BjarniHeselmans/Bat-Detectie/Docs/Attachments/esp32-s2-mini2.jpg

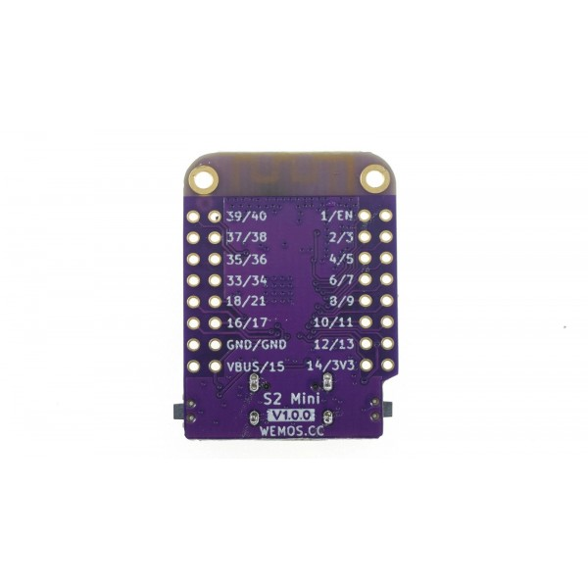
Docs/Attachments/esp32-s2-mini2.jpg
