BjarniHeselmans/Bat-Detectie/Docs/Attachments/esp32-s2-mini3.jpg

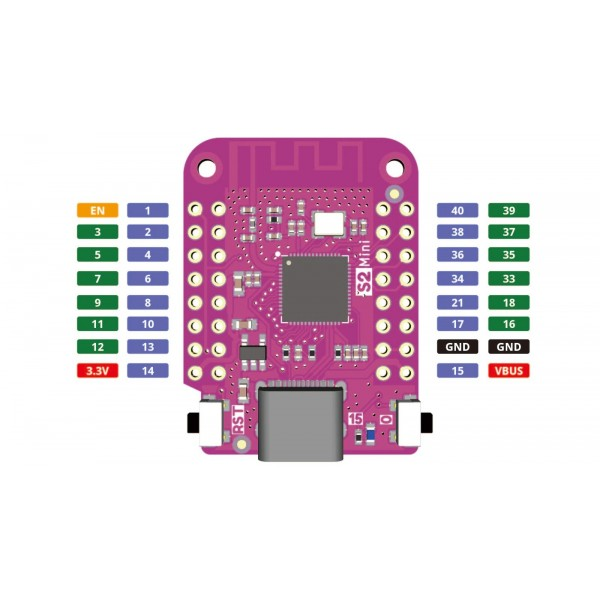
Docs/Attachments/esp32-s2-mini3.jpg
