BjarniHeselmans/Bat-Detectie/Docs/Attachments/esp32-s2-mini.jpg

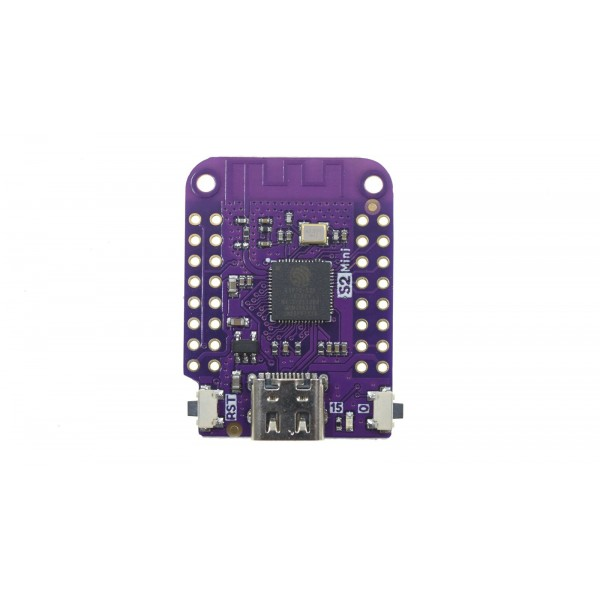
Docs/Attachments/esp32-s2-mini.jpg
