BjarniHeselmans/Bat-Detectie/Docs/Attachments/opstelling_Mini_v2.png

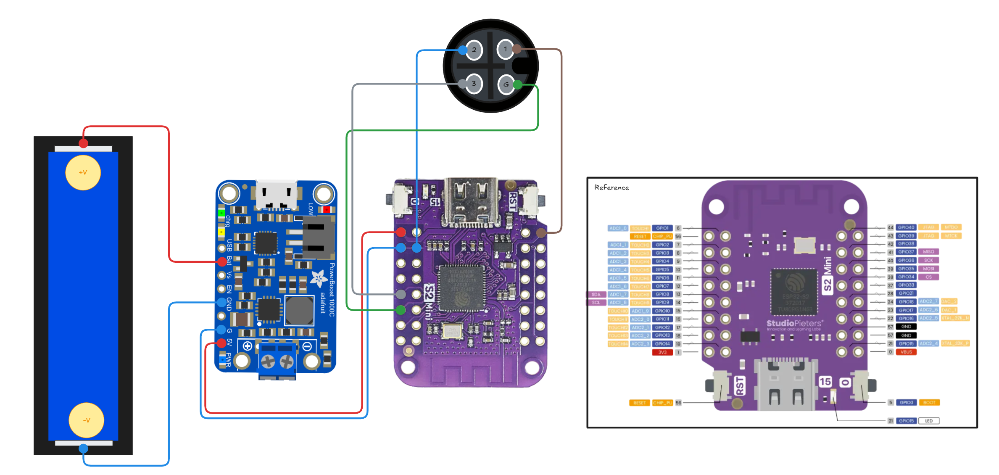
Docs/Attachments/opstelling_Mini_v2.png
