BjarniHeselmans/Bat-Detectie/Docs/Attachments/Opstelling_SHT3X.png

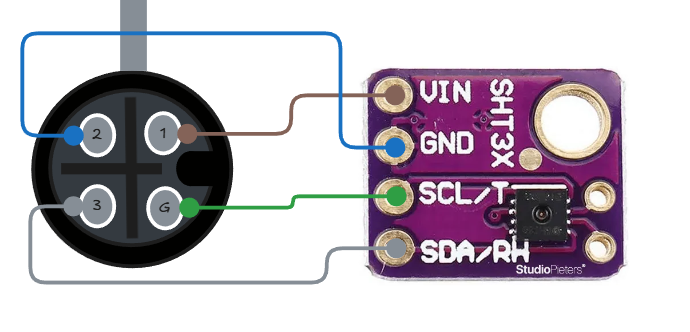
Docs/Attachments/Opstelling_SHT3X.png
