BjarniHeselmans/Bat-Detectie/Docs/Attachments/Overview.jpg

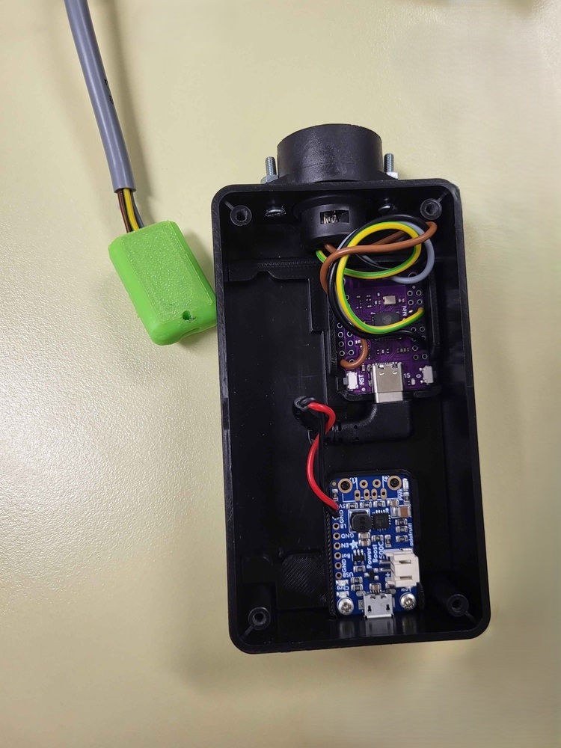
Docs/Attachments/Overview.jpg
