BjarniHeselmans/Bat-Detectie/Docs/Attachments/Power-Boost-5000.jpg

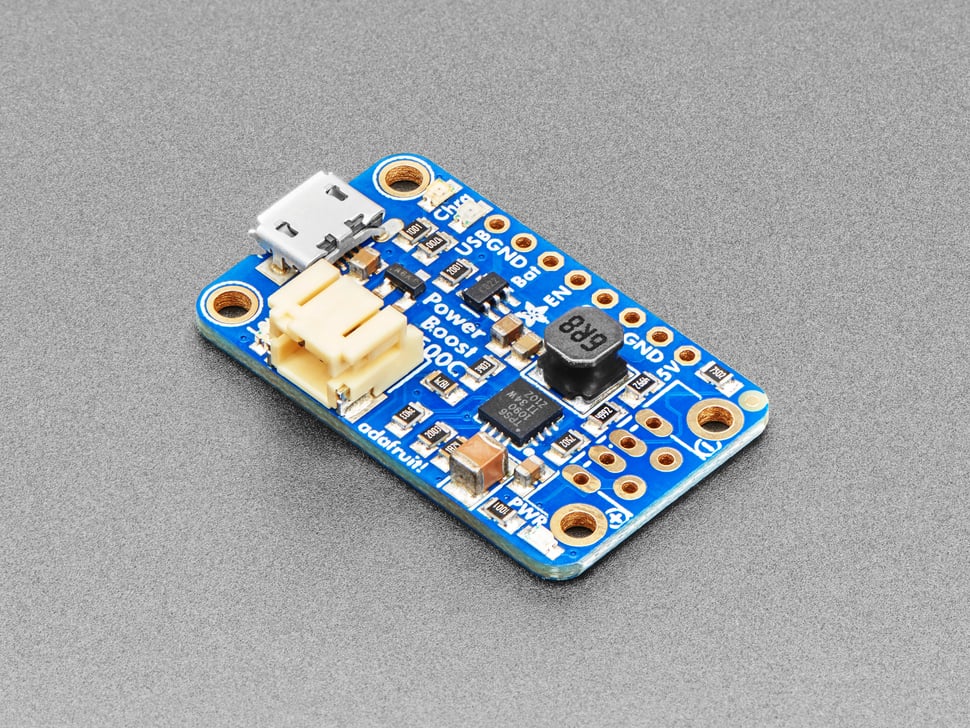
Docs/Attachments/Power-Boost-5000.jpg
