BjarniHeselmans/Bat-Detectie/Docs/Attachments/Power-Boost-50002.jpg

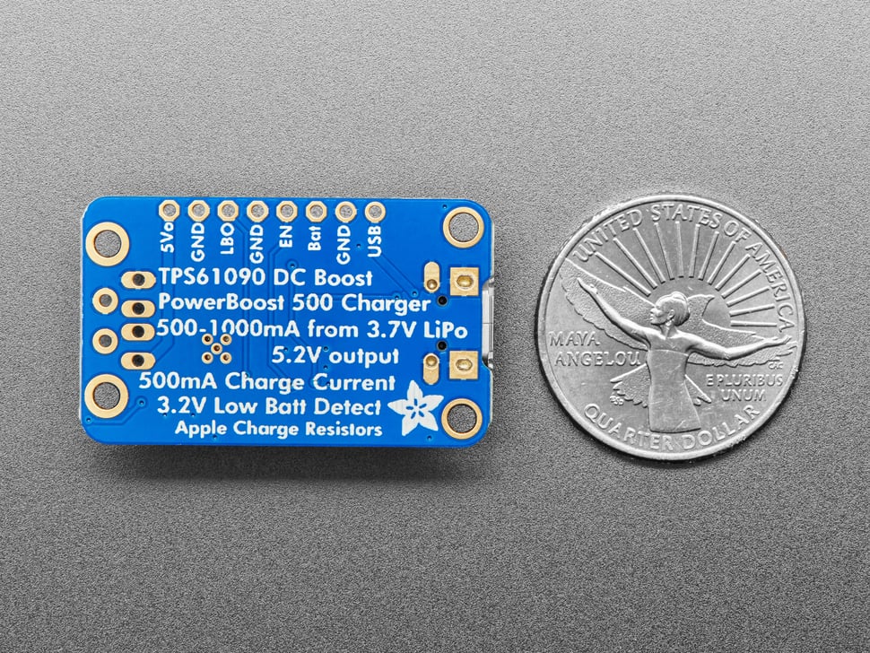
Docs/Attachments/Power-Boost-50002.jpg
