BjarniHeselmans/Bat-Detectie/Docs/Attachments/Sensor_Overzicht_Home_Assistant.png

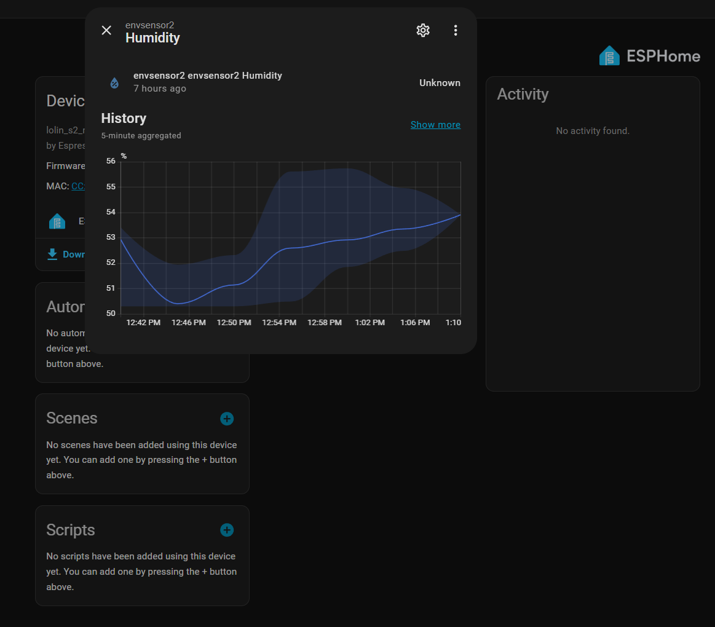
Docs/Attachments/Sensor_Overzicht_Home_Assistant.png
