BjarniHeselmans/Bat-Detectie/Docs/Attachments/SHT30.jpg

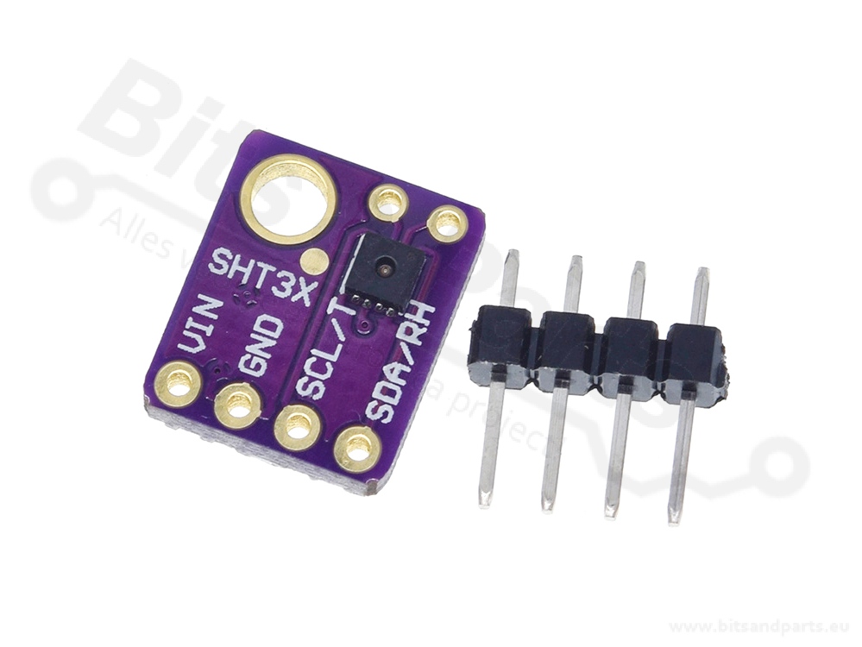
Docs/Attachments/SHT30.jpg
