BjarniHeselmans/Bat-Detectie/Docs/Attachments/SHT302.jpg

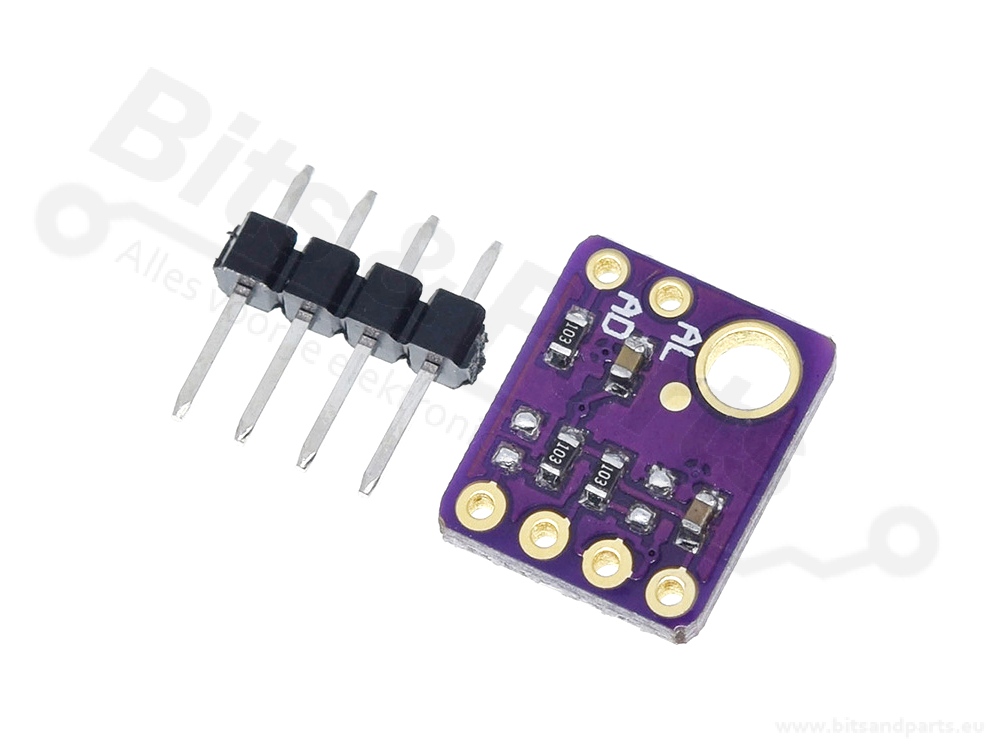
Docs/Attachments/SHT302.jpg
