BjarniHeselmans/Bat-Detectie/Docs/ElekSchem/Schema1.png

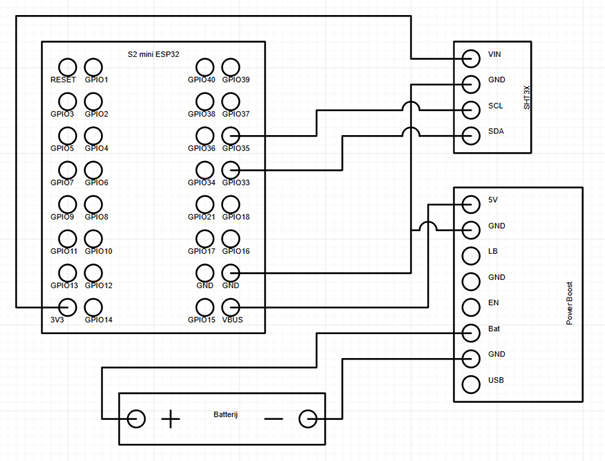
Docs/ElekSchem/Schema1.png
