BjarniHeselmans/Bat-Detectie/Src/ESPHome/image.png

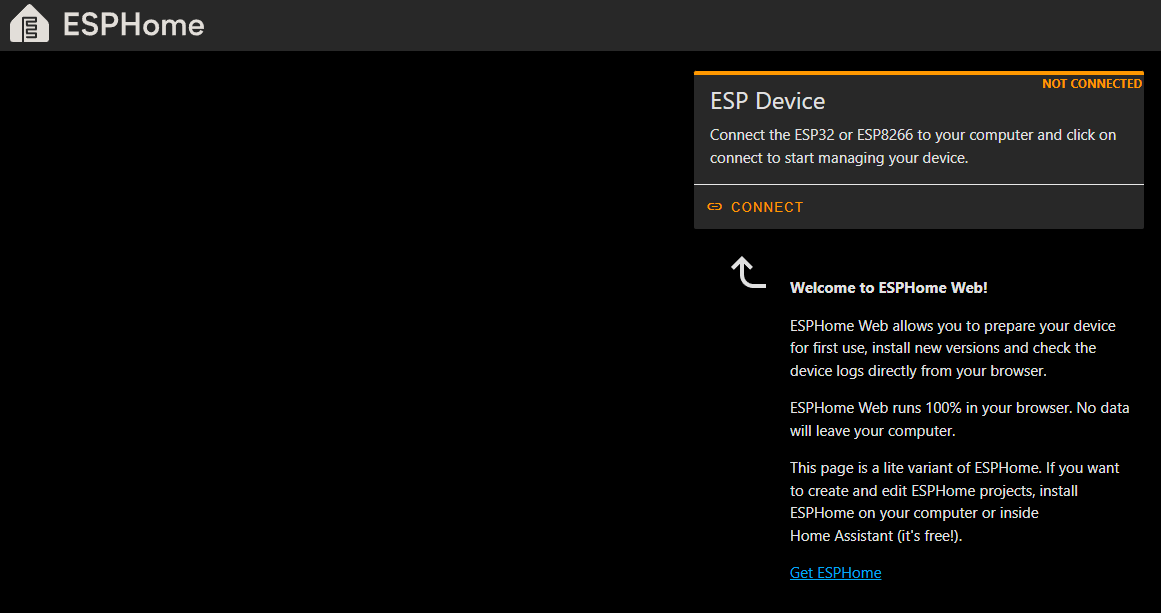
Src/ESPHome/image.png
