BjarniHeselmans/Bat-Detectie/firmware/PSOC6_test_opstelling/SD-test/bsps/TARGET_APP_CY8CPROTO-062-4343W/docs/html/board.png

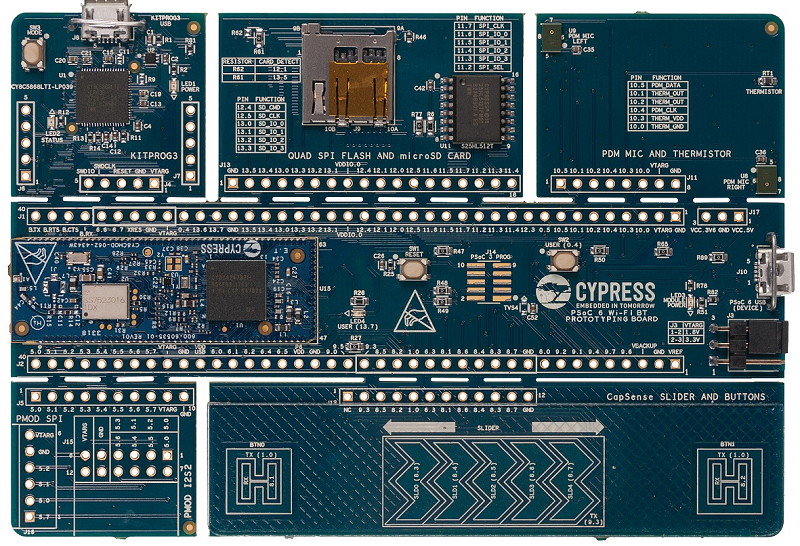
firmware/PSOC6_test_opstelling/SD-test/bsps/TARGET_APP_CY8CPROTO-062-4343W/docs/html/board.png
