BjarniHeselmans/Bat-Detectie/firmware/PSOC6_test_opstelling/SD-test/images/terminal-hello-world.png

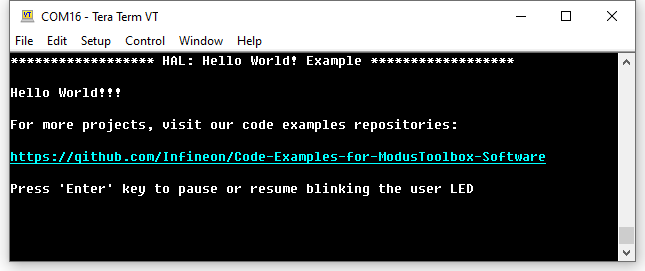
firmware/PSOC6_test_opstelling/SD-test/images/terminal-hello-world.png
